lanewinfield/yank/website/assets/images/portraits/IMAGE 2026-02-05 15:21:30.webp

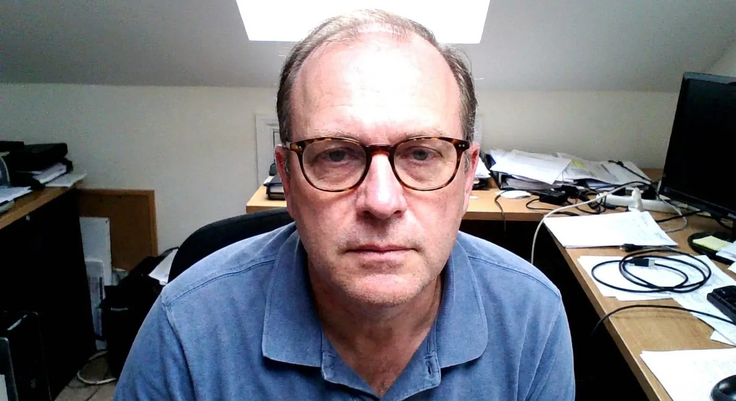
website/assets/images/portraits/IMAGE 2026-02-05 15:21:30.webp
