lanewinfield/yank/website/assets/images/portraits/IMAGE 2026-02-05 15:21:33.webp

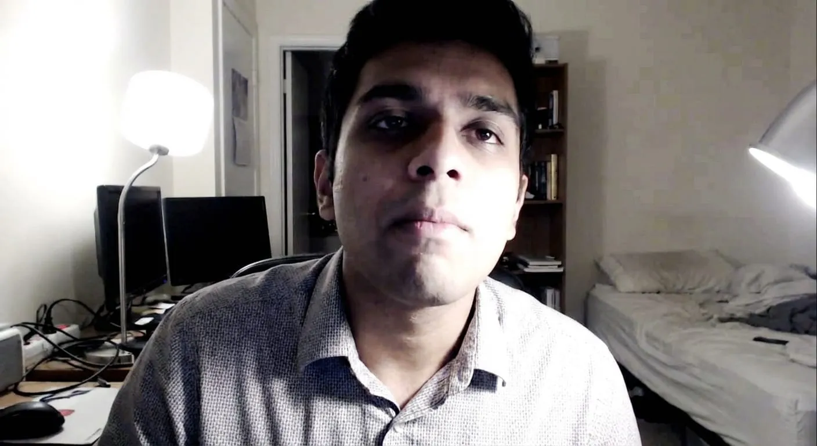
website/assets/images/portraits/IMAGE 2026-02-05 15:21:33.webp
