lanewinfield/yank/website/assets/images/portraits/IMAGE 2026-02-05 15:23:25.webp

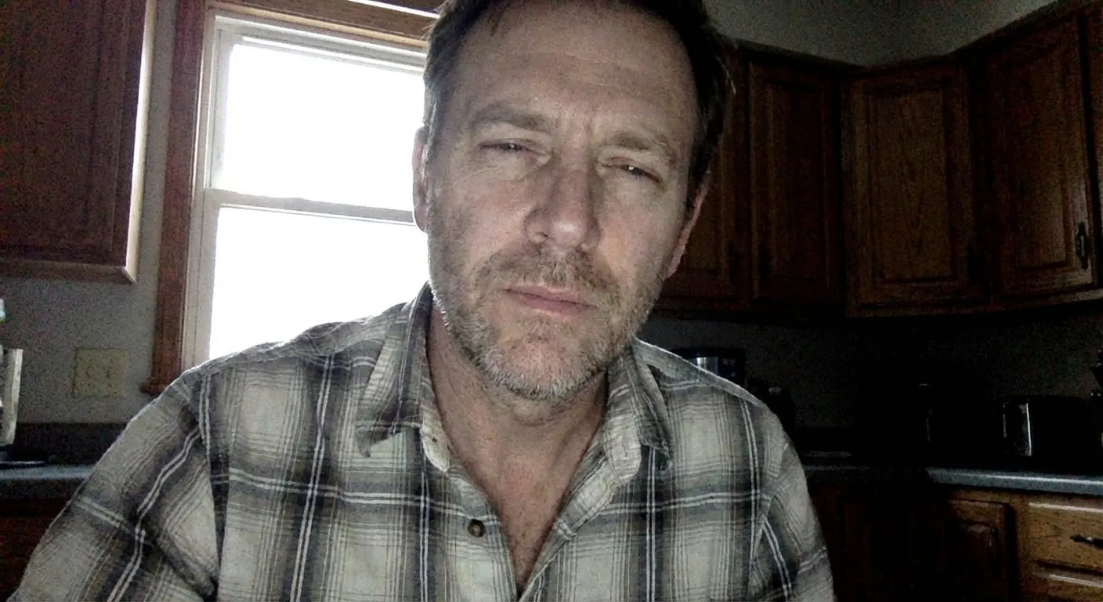
website/assets/images/portraits/IMAGE 2026-02-05 15:23:25.webp
