lanewinfield/yank/website/assets/images/portraits/IMAGE 2026-02-05 15:25:01.webp

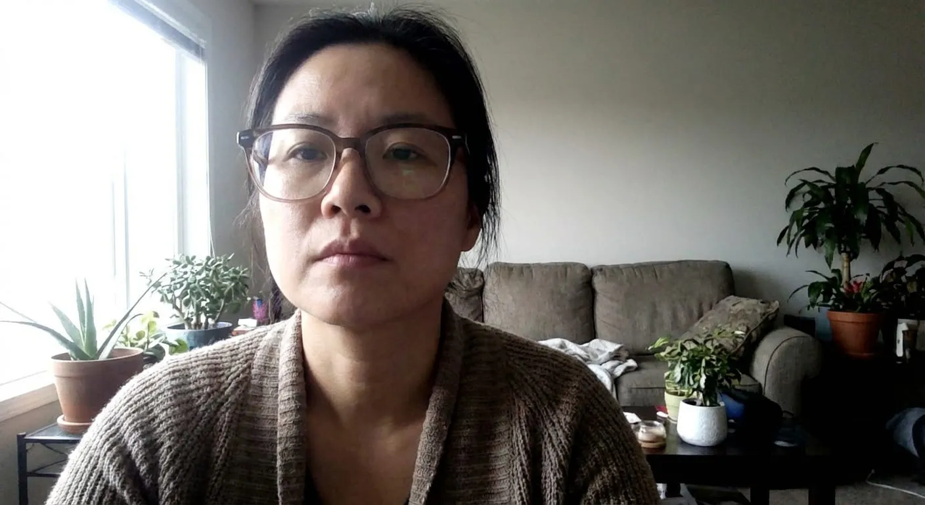
website/assets/images/portraits/IMAGE 2026-02-05 15:25:01.webp
