lanewinfield/yank/website/assets/images/portraits/IMAGE 2026-02-05 15:26:18.webp

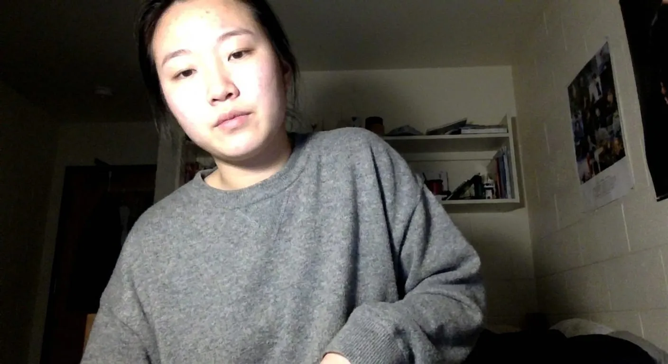
website/assets/images/portraits/IMAGE 2026-02-05 15:26:18.webp
