lanewinfield/yank/website/assets/images/portraits/IMAGE 2026-02-05 15:26:20.webp

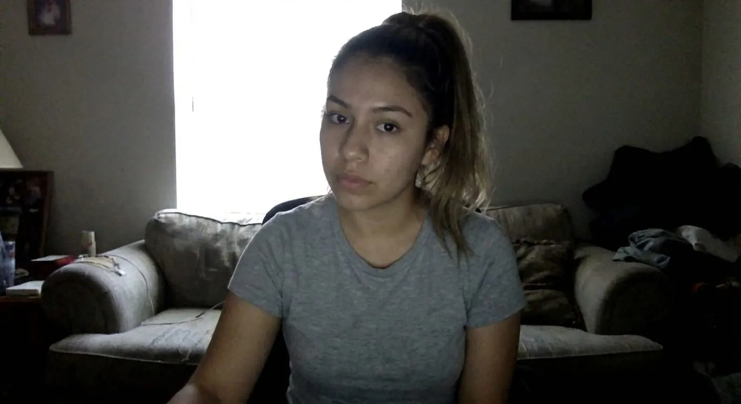
website/assets/images/portraits/IMAGE 2026-02-05 15:26:20.webp
