lanewinfield/yank/website/assets/images/portraits/IMAGE 2026-02-05 15:35:32.webp

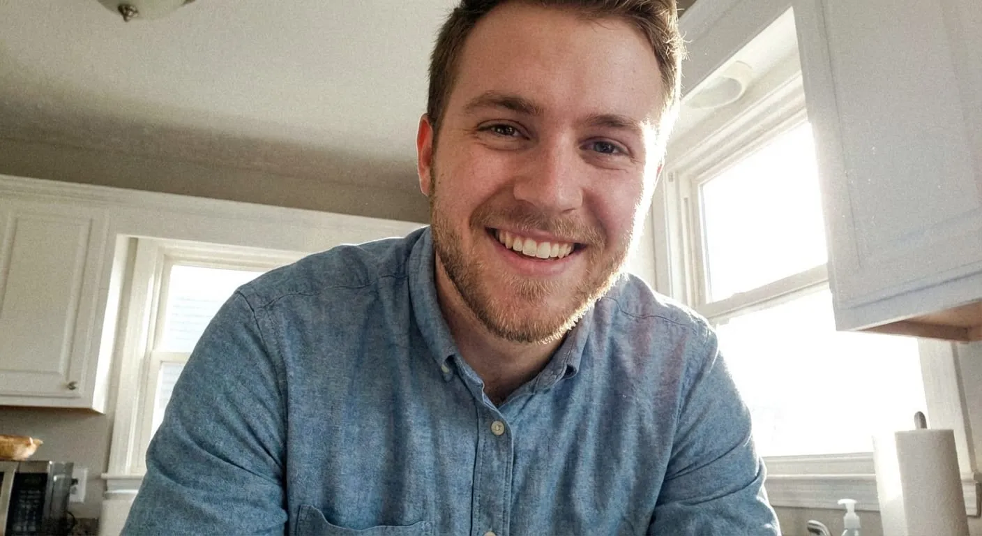
website/assets/images/portraits/IMAGE 2026-02-05 15:35:32.webp
