lanewinfield/yank/website/assets/images/portraits/IMAGE 2026-02-06 11:04:21.webp

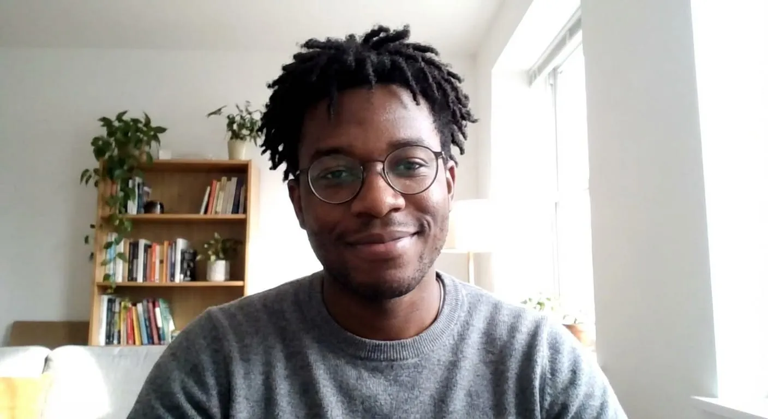
website/assets/images/portraits/IMAGE 2026-02-06 11:04:21.webp
