lanewinfield/yank/website/assets/images/portraits/IMAGE 2026-02-06 11:09:19.webp

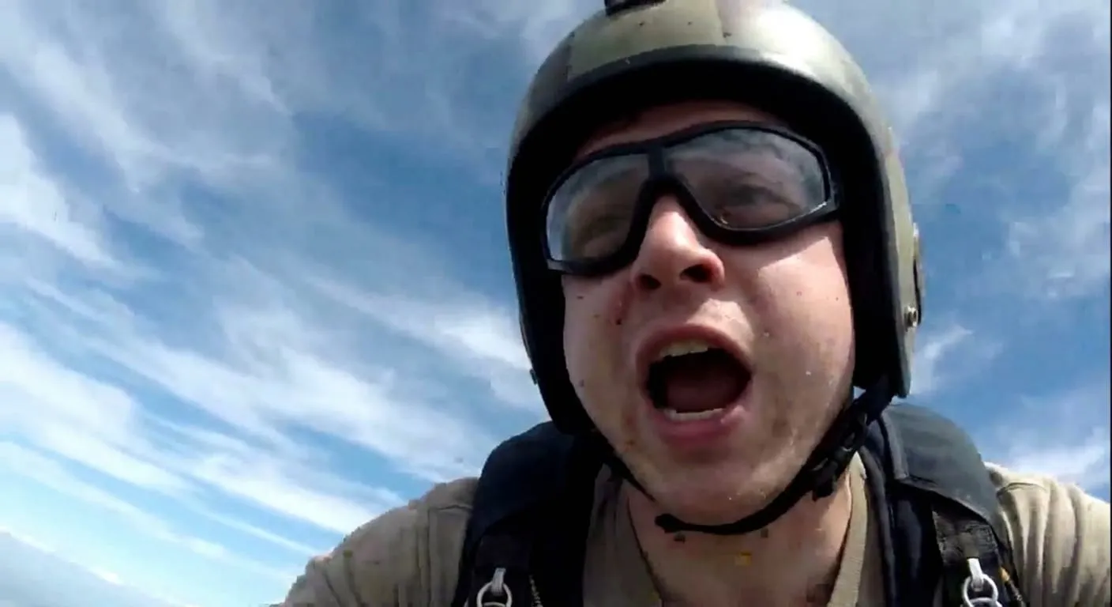
website/assets/images/portraits/IMAGE 2026-02-06 11:09:19.webp
