lanewinfield/yank/website/assets/images/portraits/IMAGE 2026-02-06 11:14:53.webp

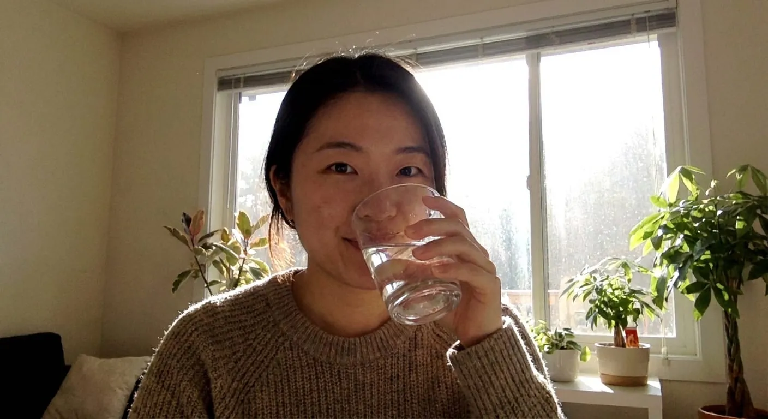
website/assets/images/portraits/IMAGE 2026-02-06 11:14:53.webp
