lanewinfield/yank/website/assets/images/portraits/IMAGE 2026-02-06 11:16:54.webp

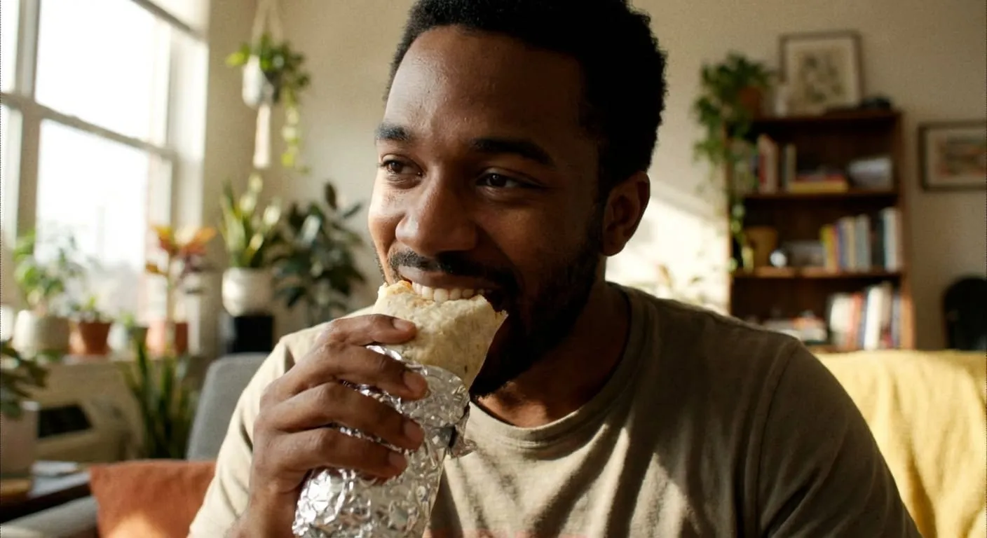
website/assets/images/portraits/IMAGE 2026-02-06 11:16:54.webp
