lanewinfield/yank/website/assets/images/portraits/me.webp

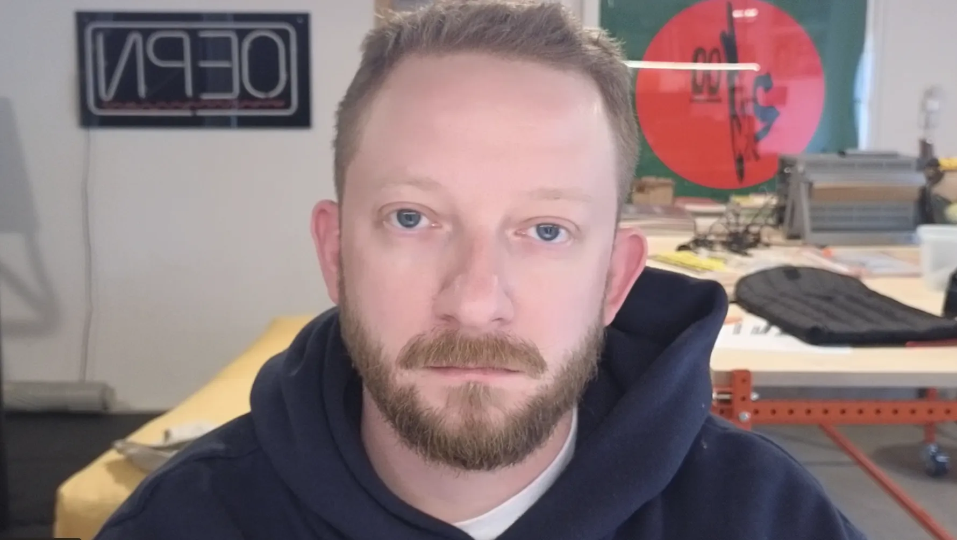
website/assets/images/portraits/me.webp
