lanewinfield/yank/website/assets/images/portraits/talker1.webp

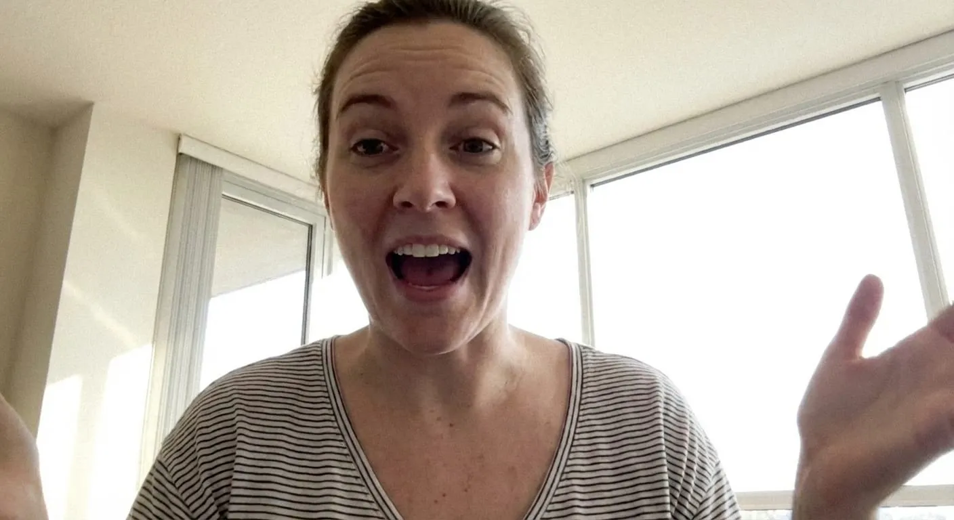
website/assets/images/portraits/talker1.webp
