lanewinfield/yank/website/assets/images/portraits/talker2.webp

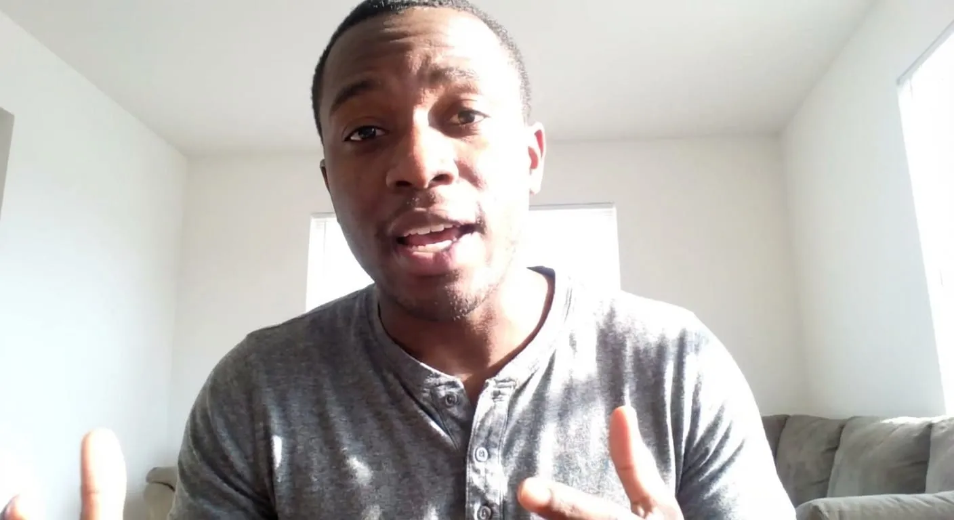
website/assets/images/portraits/talker2.webp
