lanewinfield/yank/website/assets/images/portraits/talker3.webp

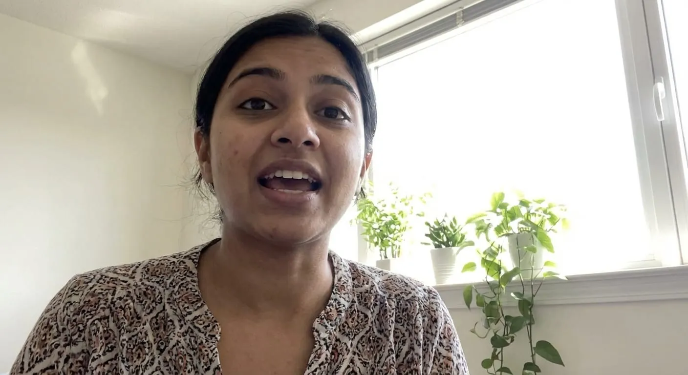
website/assets/images/portraits/talker3.webp
