lanewinfield/yank/website/assets/images/portraits/talker4.webp

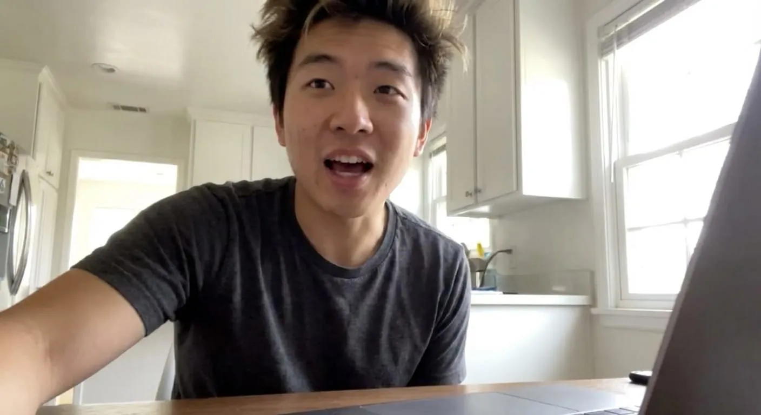
website/assets/images/portraits/talker4.webp
