lanewinfield/yank/website/assets/images/portraits/talker5.webp

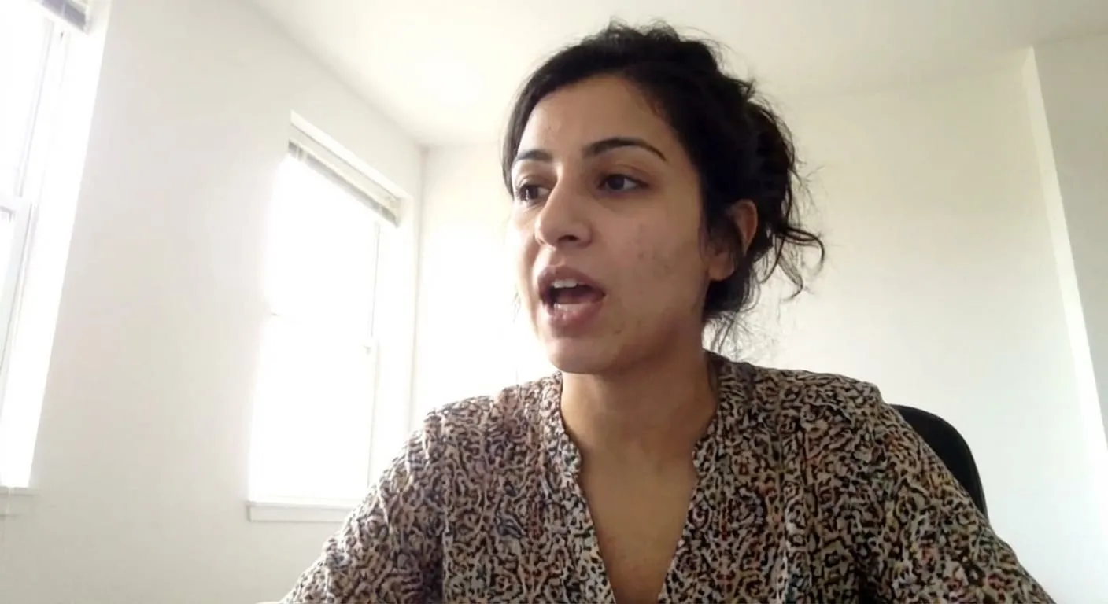
website/assets/images/portraits/talker5.webp
