lanewinfield/yank/website/assets/images/portraits/talker6.webp

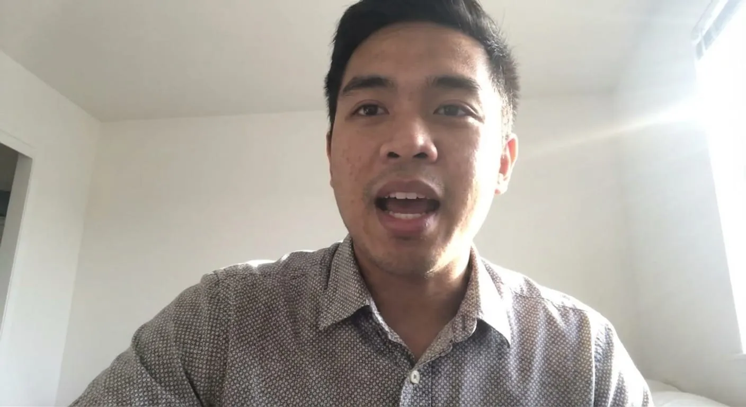
website/assets/images/portraits/talker6.webp
