lanewinfield/yank/website/assets/images/portraits/talker7.webp

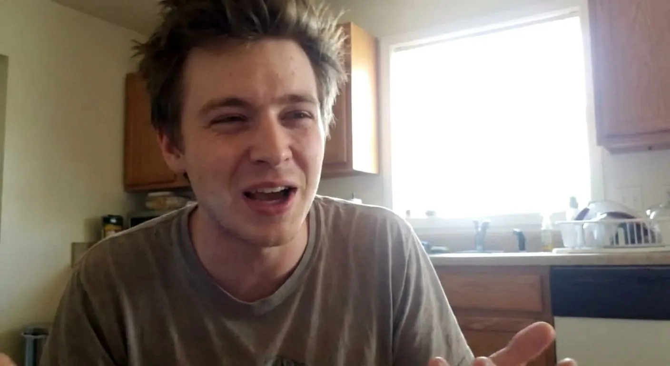
website/assets/images/portraits/talker7.webp
