lanewinfield/yank/website/assets/images/portraits/talker8.webp

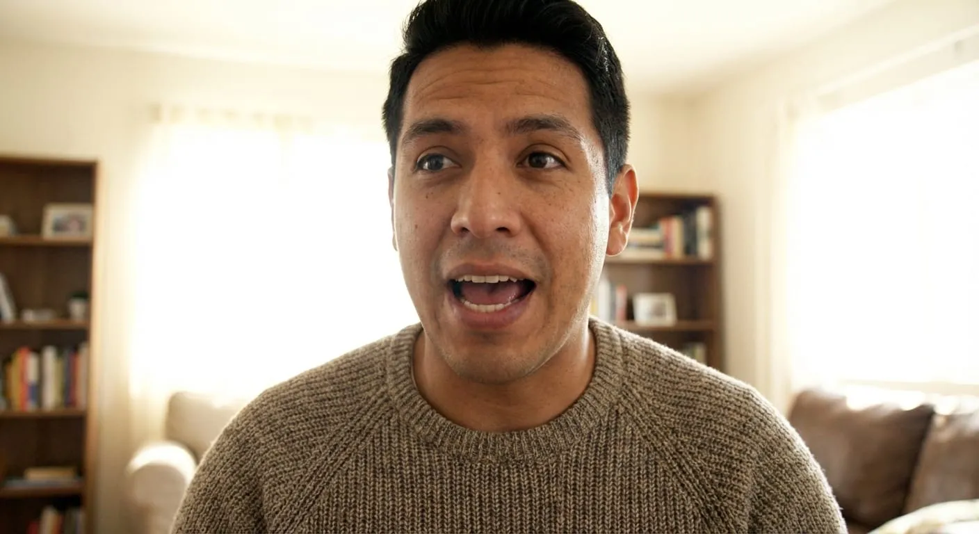
website/assets/images/portraits/talker8.webp
