lanewinfield/yank/website/assets/images/shareimage.webp

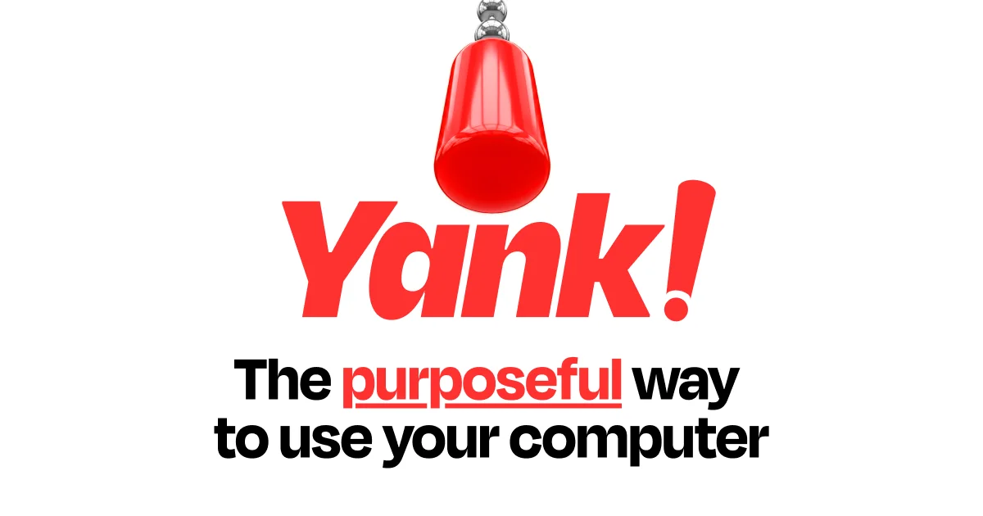
website/assets/images/shareimage.webp
